mattybrad/polymod4/code/polymod/Socket.h

#ifndef Socket_h
#define Socket_h
#include <stdint.h>
#include "modules/Module.h"

class Socket {
  public:
    Socket();
    int socketNum = -1;
    int order = -1;
    bool orderSet = false;
    Module *module;
    int param = -1;
    void process(int sampleNum);
    Socket *destSocket = nullptr;
    Socket *sourceSocket = nullptr;
    float value[Module::MAX_POLYPHONY];
    enum {UNUSED,INPUT,OUTPUT};
    int socketType = UNUSED;
     
  private:
    
};

#endif
