mattybrad/polymod4/arduino/polymod4/ModuleMidi.cpp

#include "Arduino.h"
#include "ModuleMidi.h"

ModuleMidi::ModuleMidi() {;
  for(byte i=0; i<MAX_POLYPHONY; i++) {
    _freqDC[i].amplitude(0);
    _gateDC[i].amplitude(0);
    _freqCables[i] = new AudioConnection(_freqDC[i], 0, freqOut.amplifiers[i], 0);
    _gateCables[i] = new AudioConnection(_gateDC[i], 0, gateOut.amplifiers[i], 0);
  }
  freqOut.hardcodedPoly = true;
  gateOut.hardcodedPoly = true;
}

void ModuleMidi::update() {

}

void ModuleMidi::noteOn(byte channel, byte note, byte velocity) {
  // find free note slot
  unsigned long oldestNoteTime = 4294967295;
  byte noteToUse = 0;
  bool foundFreeNote = false;
  byte i;
  for(i=0; i<MAX_POLYPHONY; i++) {
    if(!_notes[i].noteDown && _notes[i].timeEnded < oldestNoteTime) {
      oldestNoteTime = _notes[i].timeEnded;
      noteToUse = i;
      foundFreeNote = true;
    }
  }
  if(!foundFreeNote) {
    // if no free note slot, use lowest note
    byte lowestNoteNum = 255;
    for(i=0; i<MAX_POLYPHONY; i++) {
      if(_notes[i].noteNum <= lowestNoteNum) {
        lowestNoteNum = _notes[i].noteNum;
        noteToUse = i;
      }
    }
  }
  _notes[noteToUse].noteDown = true;
  _notes[noteToUse].noteNum = note;
  _notes[noteToUse].timeStarted = millis();
  _notes[noteToUse].timeEnded = 4294967295;
  _freqDC[noteToUse].amplitude((note-69)/12.0/10.0); // 12.0 because 12 notes per octave, 10.0 because 10 octave range (over -1.0 to +1.0)
  _gateDC[noteToUse].amplitude(1.0);
}

void ModuleMidi::noteOff(byte channel, byte note, byte velocity) {
  // find any active notes matching note off note
  byte i;
  for(i=0; i<MAX_POLYPHONY; i++) {
    if(_notes[i].noteDown && _notes[i].noteNum == note) {
      _notes[i].noteDown = false;
      _notes[i].timeEnded = millis();
      _gateDC[i].amplitude(0.0);
    }
  }
}
