mattybrad/polymod4/arduino/polymod4/ModuleSine.cpp

#include "Arduino.h"
#include "ModuleSine.h"

ModuleSine::ModuleSine() {
  for(byte i=0; i<MAX_POLYPHONY; i++) {
    _sineOsc[i].amplitude(1.0);
    _sineOsc[i].frequency(0.5+2*i);
    _sineOscCables[i] = new AudioConnection(_sineOsc[i], 0, audioOut.amplifiers[i], 0);
    //audioOut.hardcodedPoly = true;
  }
}

void ModuleSine::update() {

}
