mattybrad/polymod4/arduino/polymod4/SocketInput.h

#ifndef SocketInput_h
#define SocketInput_h
#include "Arduino.h"
#include "Globals.h"
#include <Audio.h>
 
class SocketInput {
  public:
    SocketInput();
    AudioAmplifier amplifiers[MAX_POLYPHONY];
    int connNum = -1;
  private:
    
};

#endif
