mattybrad/polymod4/arduino/polymod4/ModuleVCO.h

#ifndef ModuleVCO_h
#define ModuleVCO_h
#include "Arduino.h"
#include "Module.h"
#include "AnalogControl.h"

class ModuleVCO : public Module {
  public:
    ModuleVCO();
    virtual void update();
    SocketOutput audioOut;
    SocketInput freqModIn;
    byte analogPin = 14;
  private:
    AnalogControl _freqControl;
    AudioSynthWaveformModulated _osc[MAX_POLYPHONY];
    AudioMixer4 _modMixer[MAX_POLYPHONY];
    AudioConnection* _oscCables[MAX_POLYPHONY];
    AudioConnection* _modCables1[MAX_POLYPHONY];
    AudioConnection* _modCables2[MAX_POLYPHONY];
    AudioConnection* _modCables3[MAX_POLYPHONY];
};

#endif
