mattybrad/polymod4/arduino/polymod4/Module.h

#ifndef Module_h
#define Module_h
#include "Arduino.h"
#include "SocketOutput.h"
#include "SocketInput.h"
#include "Globals.h"
#include <Audio.h>

class Module {
  public:
    Module();
    
    
  private:
    
    
};

#endif
