mattybrad/polymod4/arduino/polymod4/ModuleSine.h

#ifndef ModuleSine_h
#define ModuleSine_h
#include "Arduino.h"
#include "Module.h"

class ModuleSine : public Module {
  public:
    ModuleSine();
    virtual void update();
    SocketOutput audioOut;
  private:
    AudioSynthWaveformSine _sineOsc[MAX_POLYPHONY];
    AudioConnection* _sineOscCables[MAX_POLYPHONY];
    
};

#endif
